leo-buono/Game-Hardware/Assignment 3/Images of Device and Electronics/Electronics 3.jpg

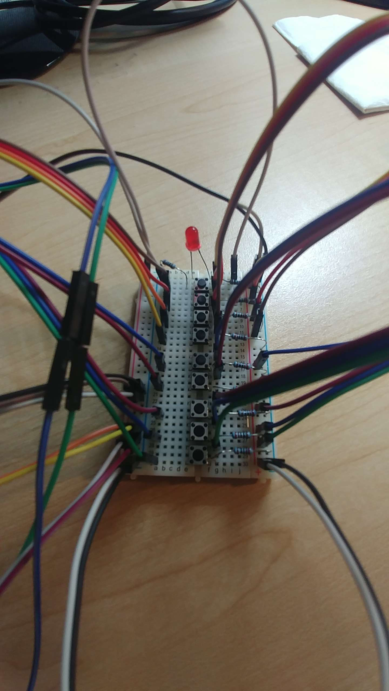
Assignment 3/Images of Device and Electronics/Electronics 3.jpg
