leo-buono/Game-Hardware/Assignment 3/Images of Device and Electronics/3D Print 5.jpg

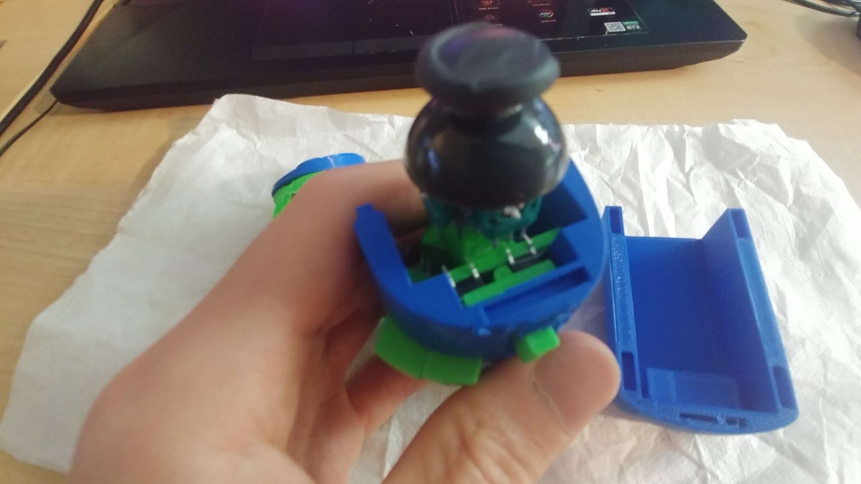
Assignment 3/Images of Device and Electronics/3D Print 5.jpg
